changgeruoxiao/hagent/doc/extracted/figures/AN4938_硬件开发入门_p12.png

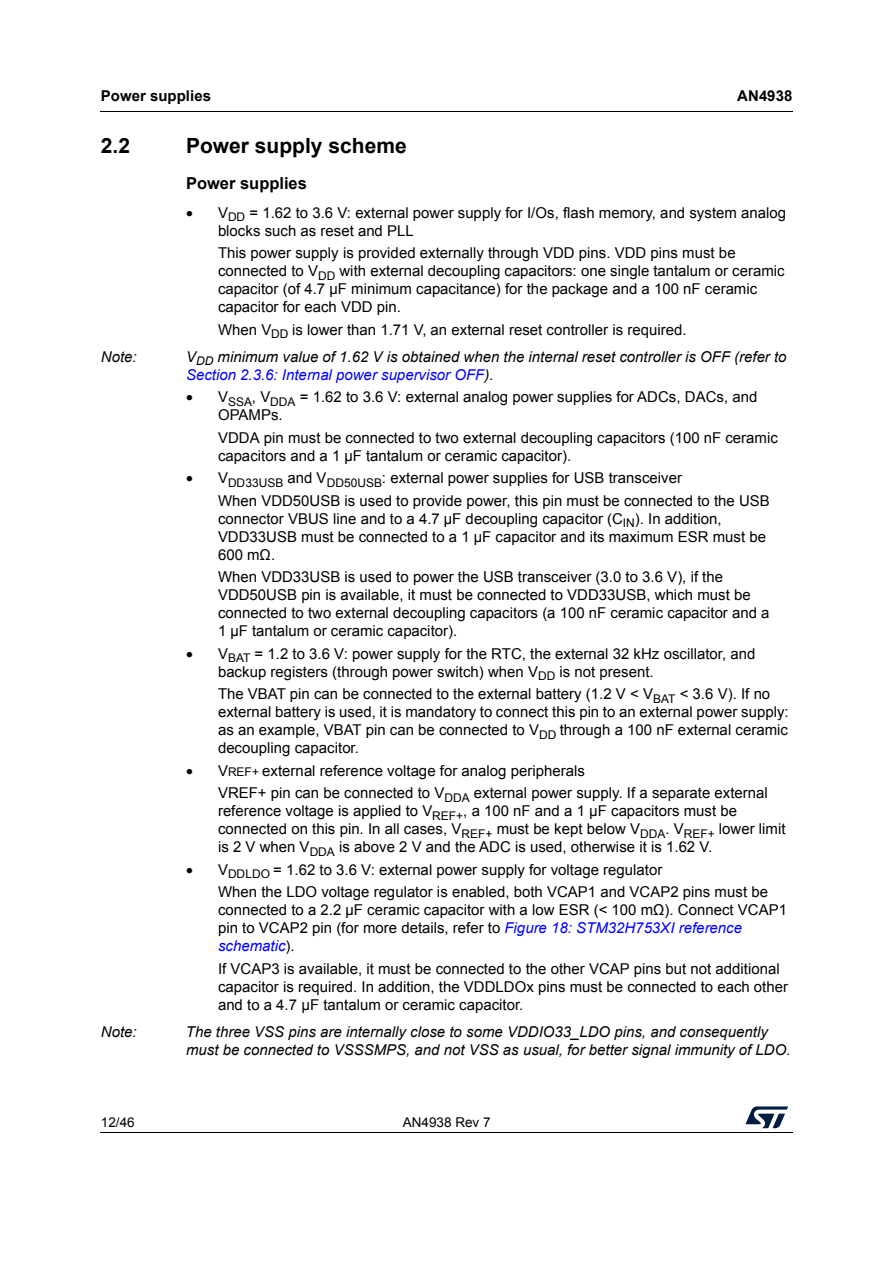
doc/extracted/figures/AN4938_硬件开发入门_p12.png
