changgeruoxiao/hagent/doc/extracted/figures/NUCLEO-H743ZI2_MB1364_官方原理图_p4.png

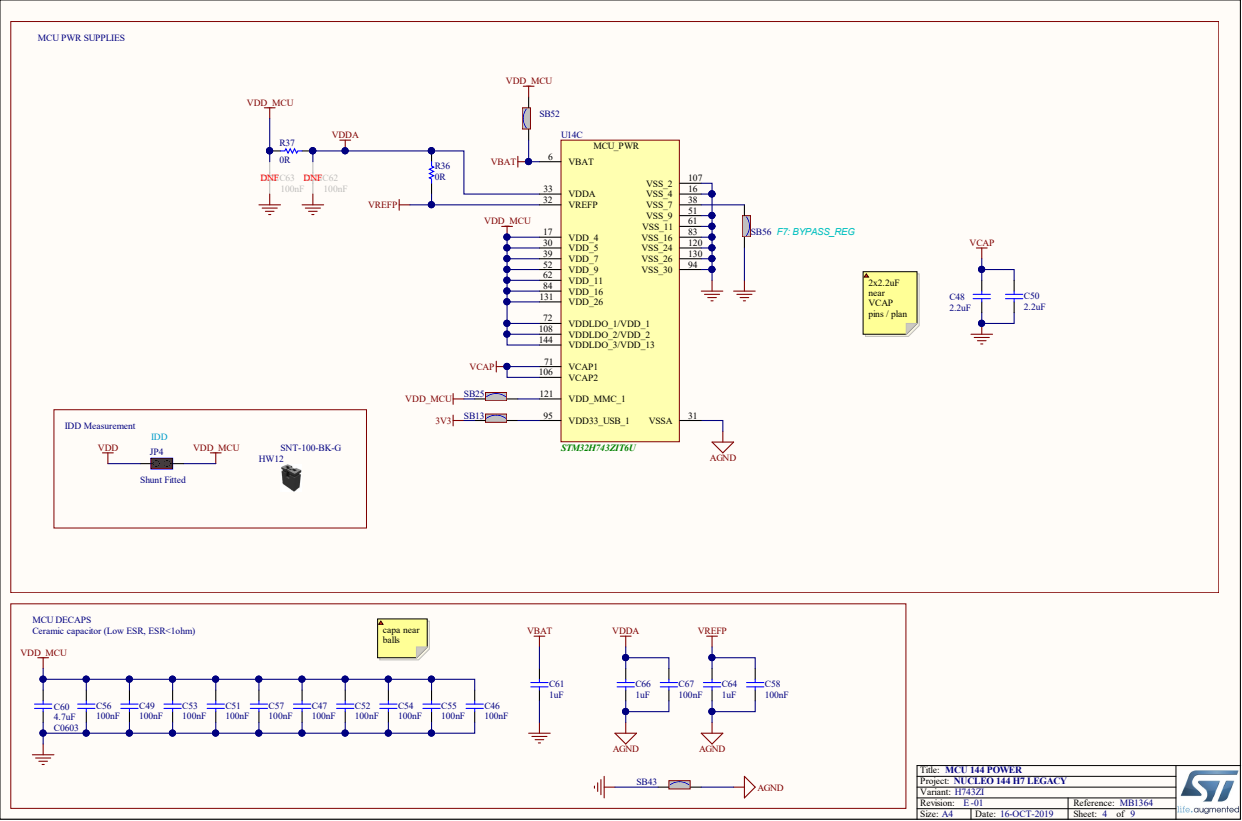
doc/extracted/figures/NUCLEO-H743ZI2_MB1364_官方原理图_p4.png
