changgeruoxiao/hagent/doc/extracted/figures/TPS54331_数据手册_p25.png

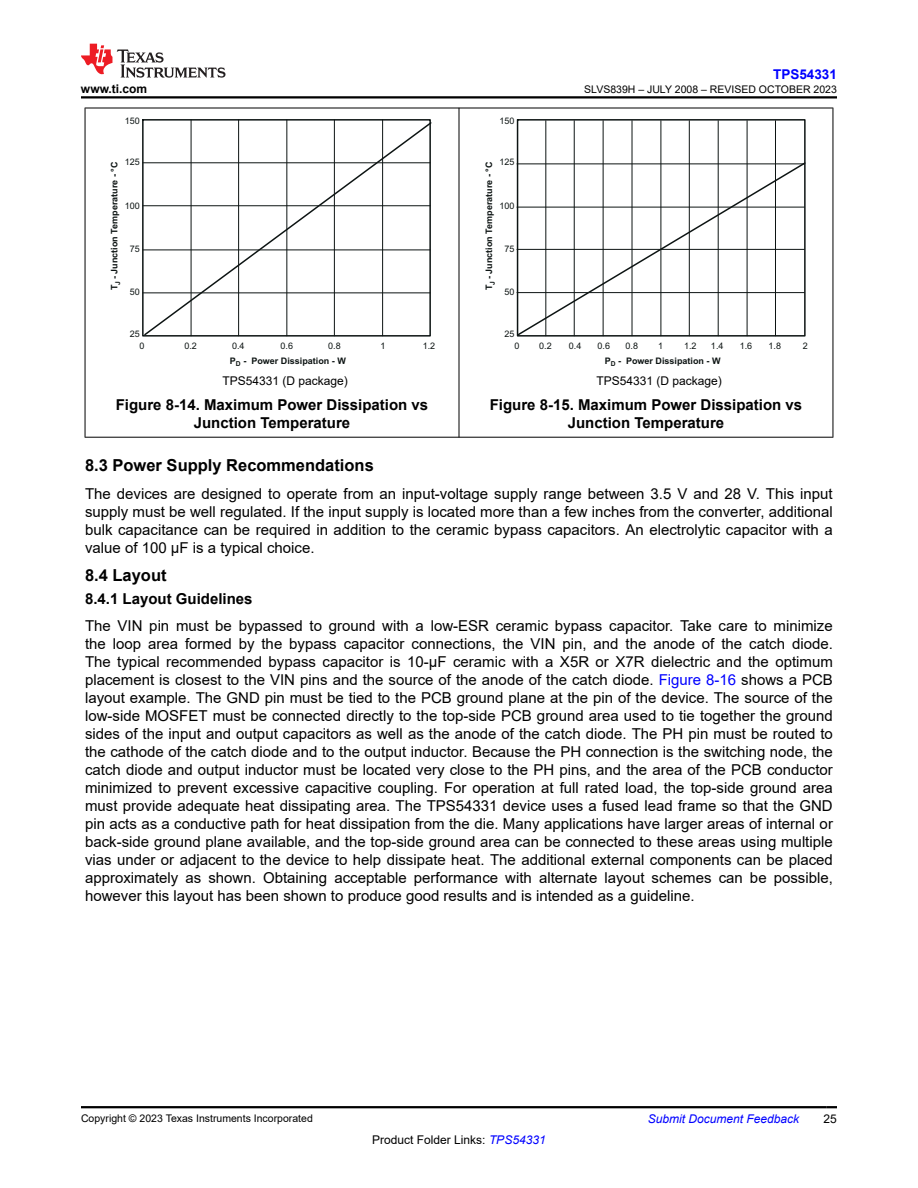
doc/extracted/figures/TPS54331_数据手册_p25.png
